LaboratorioGluon/Rc-Test-Bench/CodigoFuente/RcTestBench/include/basicConfig.h

#ifndef __BASICCONF_H__
#define  __BASICCONF_H__

//extern ADC_HandleTypeDef hadc1;
//extern DMA_HandleTypeDef hdma_adc1;

void SystemClock_Config(void);

//void Init_ADC(void);

#endif // __BASICCONF_H__
