LaboratorioGluon/Rc-Test-Bench/CodigoFuente/RcTestBench/src/Comms.cpp

#include "Comms.h"

UART_HandleTypeDef huart1;

static void MX_USART1_UART_Init(void)
{

  huart1.Instance = USART1;
  huart1.Init.BaudRate = 57600;
  huart1.Init.WordLength = UART_WORDLENGTH_8B;
  huart1.Init.StopBits = UART_STOPBITS_1;
  huart1.Init.Parity = UART_PARITY_NONE;
  huart1.Init.Mode = UART_MODE_TX_RX;
  huart1.Init.HwFlowCtl = UART_HWCONTROL_NONE;
  huart1.Init.OverSampling = UART_OVERSAMPLING_16;
  HAL_UART_Init(&huart1);

  HAL_NVIC_SetPriority(USART1_IRQn, 0, 0);
  HAL_NVIC_EnableIRQ(USART1_IRQn);
  __HAL_UART_ENABLE_IT(&huart1, UART_IT_RXNE);

}

void InitUartGpio(void){
    __HAL_RCC_GPIOA_CLK_ENABLE();

    GPIO_InitTypeDef GPIO_InitStruct = {0};

    GPIO_InitStruct.Pin = GPIO_PIN_9;
    GPIO_InitStruct.Mode = GPIO_MODE_AF_PP;
    GPIO_InitStruct.Speed = GPIO_SPEED_FREQ_HIGH;
    HAL_GPIO_Init(GPIOA, &GPIO_InitStruct);

    GPIO_InitStruct.Pin = GPIO_PIN_10;
    GPIO_InitStruct.Mode = GPIO_MODE_INPUT;
    GPIO_InitStruct.Pull = GPIO_NOPULL;
    HAL_GPIO_Init(GPIOA, &GPIO_InitStruct);

}

void InitUART(){

    __HAL_RCC_USART1_CLK_ENABLE();


    MX_USART1_UART_Init();
    InitUartGpio();
}
